AzonInc/Doorman/docs/de/index.md

---
# https://vitepress.dev/reference/default-theme-home-page
layout: home

hero:
  name: Doorman
  text: Gateway für TCS und Koch intercoms
  tagline: Für ESPHome und Home Assistant gemacht
  image:
    src: /enclosure.png
    alt: Doorman
  actions:
    - theme: brand
      text: Was ist Doorman?
      link: /de/guide/what-is-doorman
    - theme: alt
      text: Quickstart
      link: /de/guide/getting-started

    - theme: alt
      text: GitHub
      link: https://github.com/azoninc/doorman

features:
  - icon: 🚀
    title: Leistungsfähig
    details: Angetrieben vom ESP32-S3 mit Dual-Core-CPU, integriertem PSRAM und Bluetooth, vereint er beeindruckende Leistung mit vielseitiger Einsatzfähigkeit.

  - icon: 🤏
    title: Kompakt
    details: Dank seines durchdachten Designs findet er fast überall Platz und ist somit ideal für eine Vielzahl von Installationsszenarien geeignet.

  - icon: ✨
    title: Erweiterbar
    details: Zwei zusätzliche GPIOs und ein externer Button ermöglichen eine flexible und einfache Erweiterung mit eigenen Sensoren und Geräten, z. B. über I²C.

  - icon: 🎉
    title: Kompatibel
    details: Das Solid-State-Relais ermöglicht das Schalten von bis zu 40V (max. 2,5A) und ist somit ideal für die Integration in ältere Gegensprechanlagen geeignet.
---
