AzonInc/Doorman/.github/images/pcb_bottom_dark.png

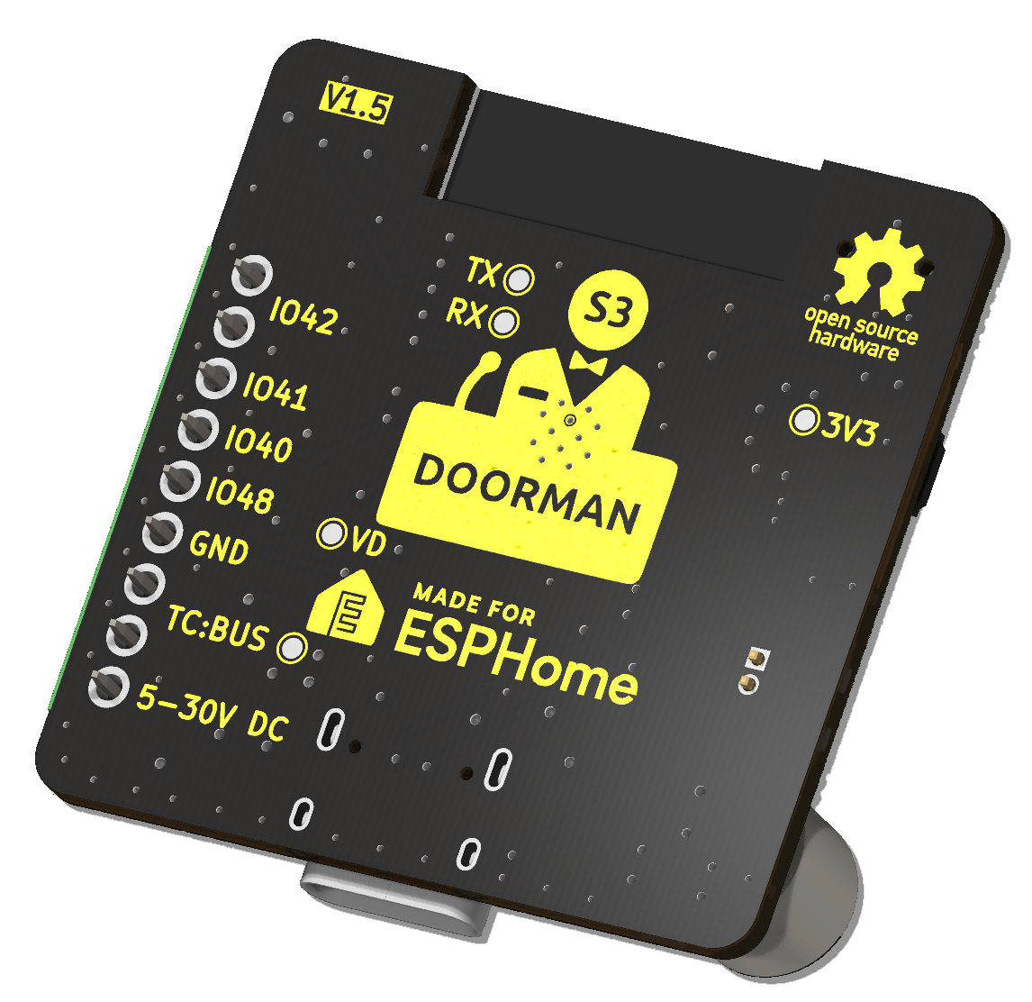
.github/images/pcb_bottom_dark.png
