AzonInc/Doorman/.github/images/pcb_top_dark.png

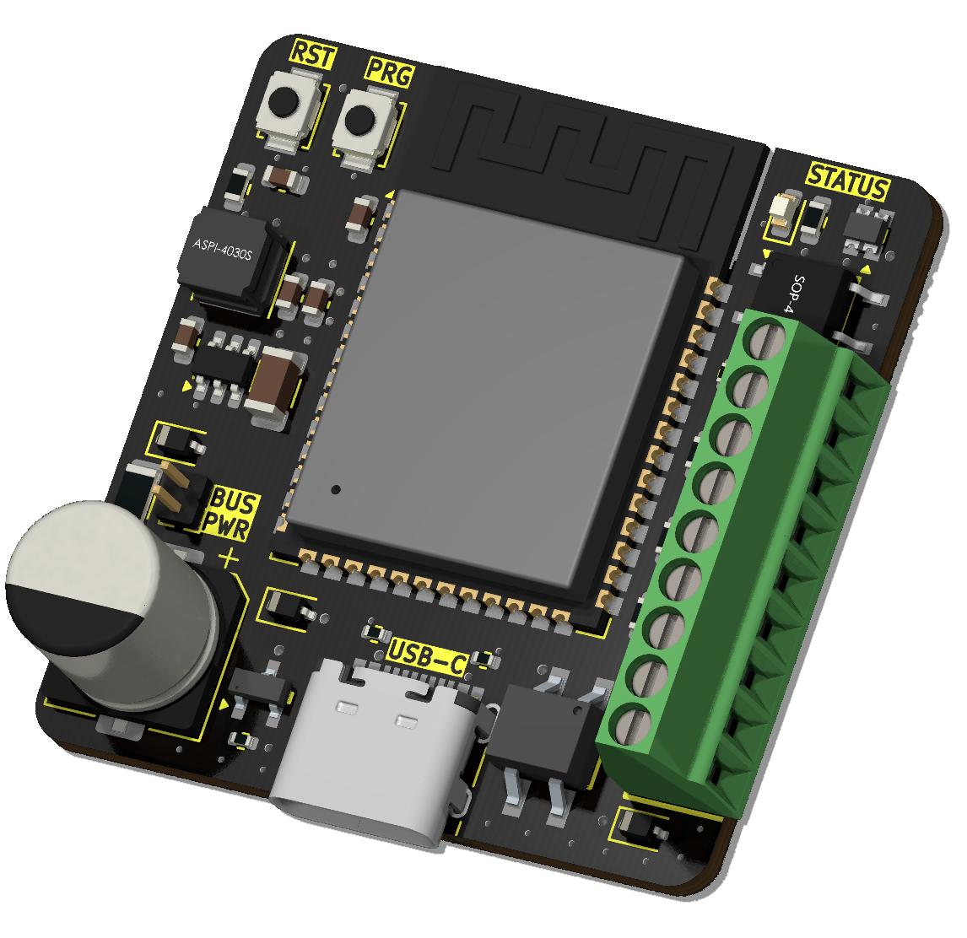
.github/images/pcb_top_dark.png
